sarpharaj-09/micromouse-line-follower/Arduino_Nano/pcb_v1/New folder/lineMazeSolver-Edge_Cuts.pdf

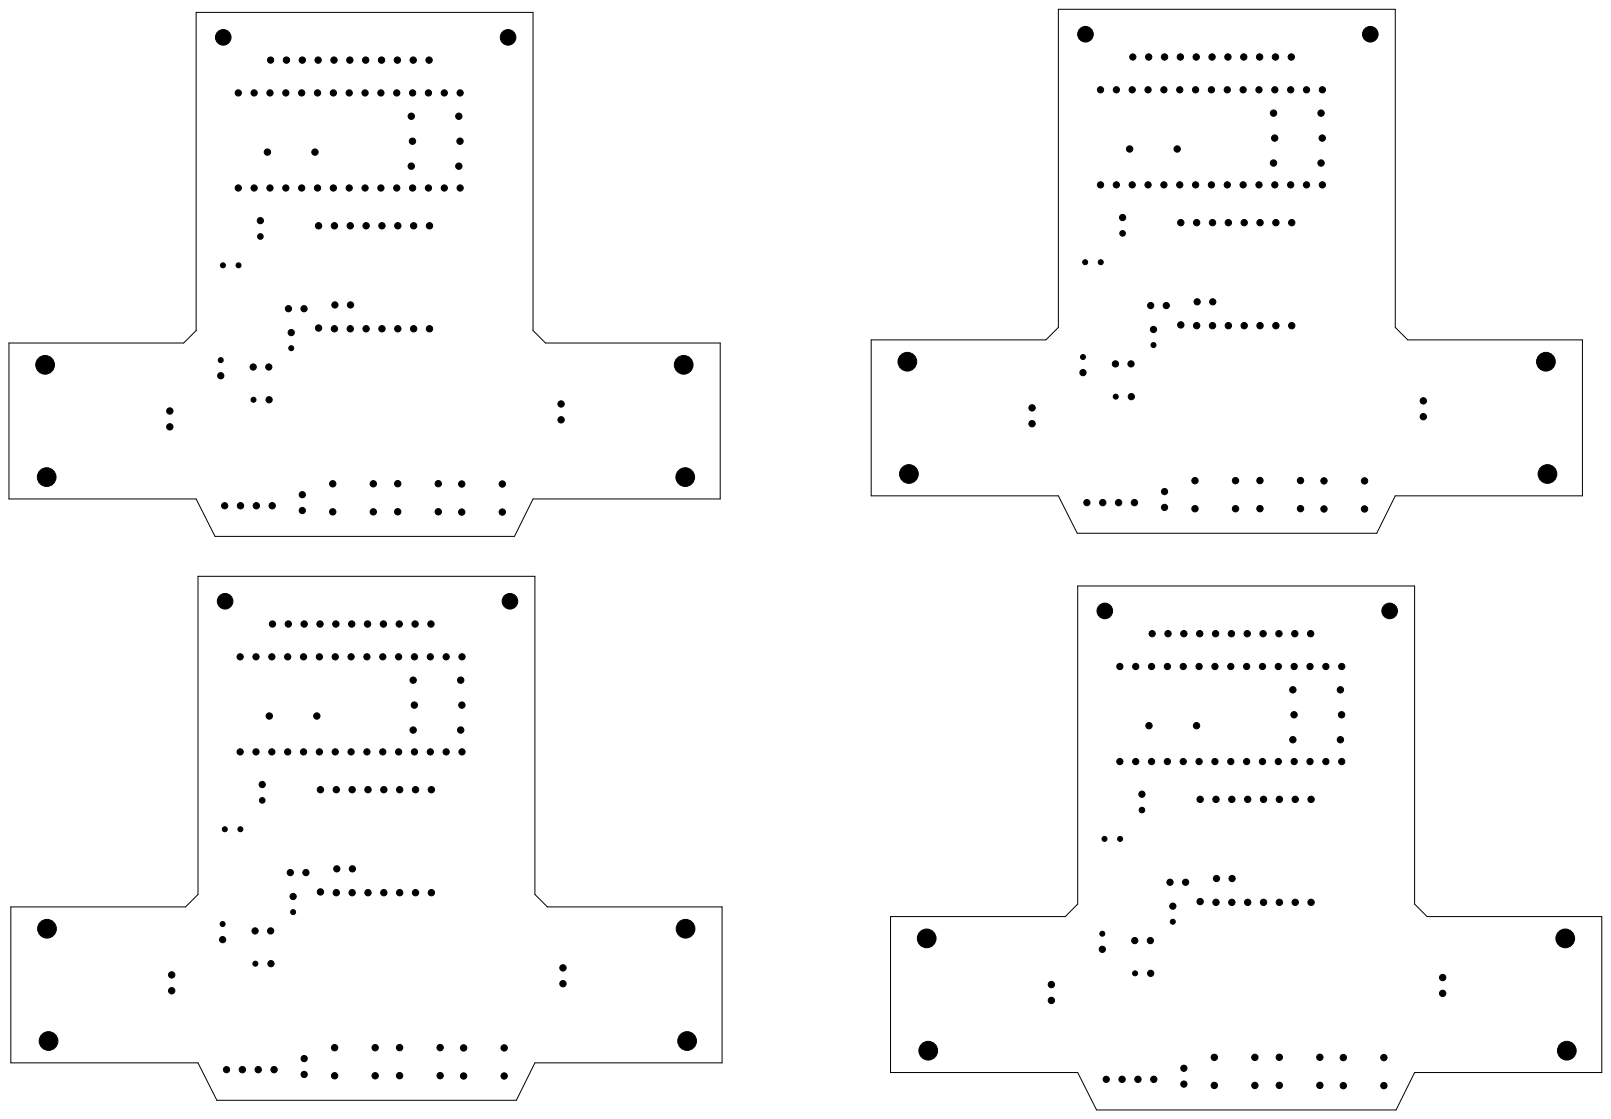
[picture p13: page 1]
