sarpharaj-09/micromouse-line-follower/Arduino_Nano/pcb_v1/New folder/lineMazeSolver-F_Cu.pdf

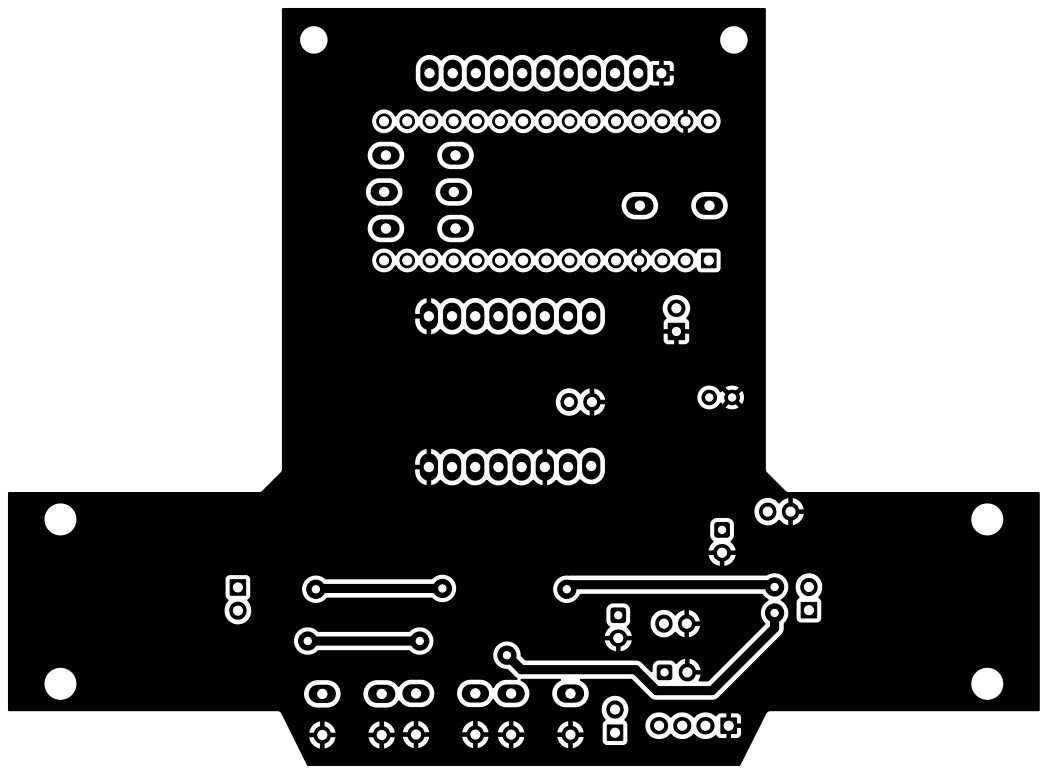
[picture p14: page 1]
